ccadic/HackZeGarage/images/20220101_232448.jpg

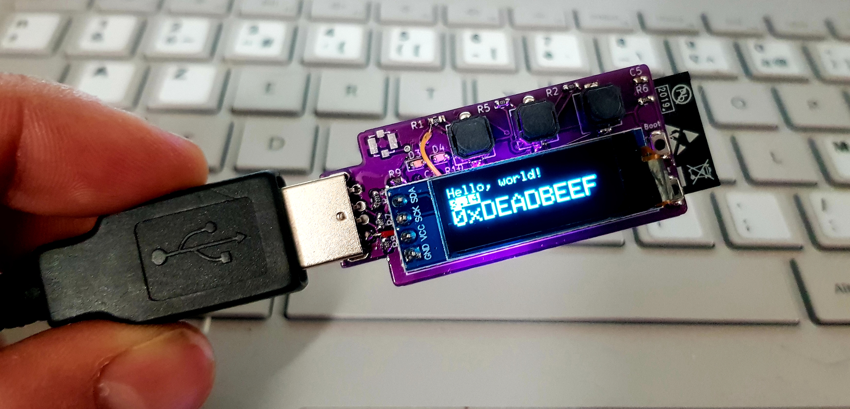
images/20220101_232448.jpg
