ccadic/HackZeGarage/images/20220101_232506.jpg

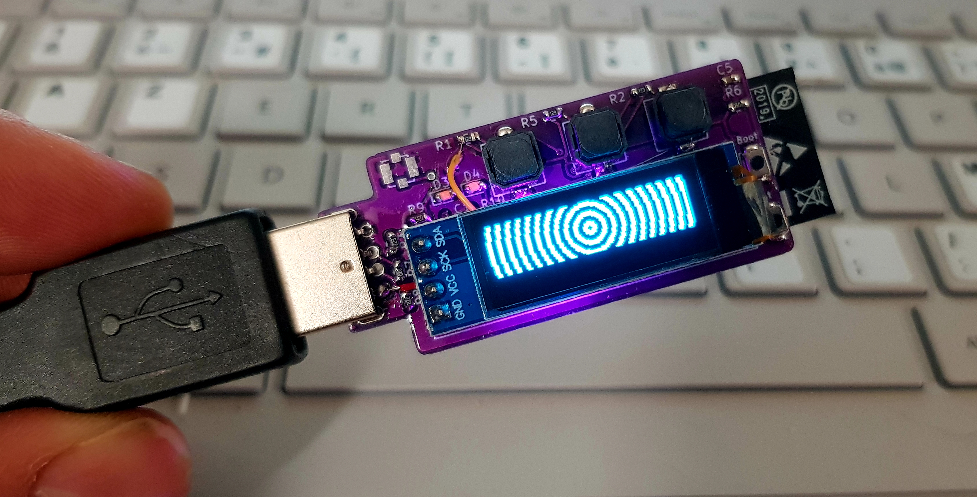
images/20220101_232506.jpg
