ccadic/HackZeGarage/images/20220101_232624.jpg

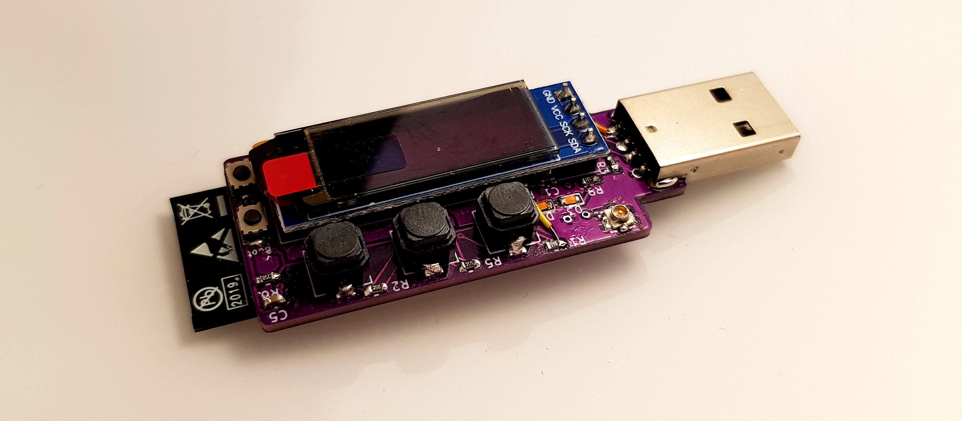
images/20220101_232624.jpg
