ccadic/HackZeGarage/images/20220101_232640.jpg

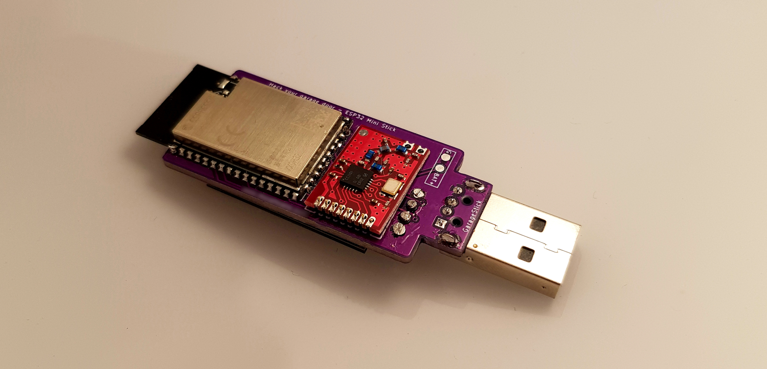
images/20220101_232640.jpg
