ccadic/HackZeGarage/images/20220102_003041.jpg

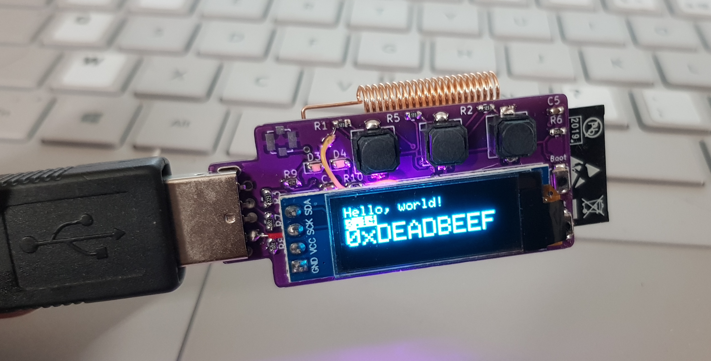
images/20220102_003041.jpg
