ccadic/HackZeGarage/images/20220102_003132.jpg

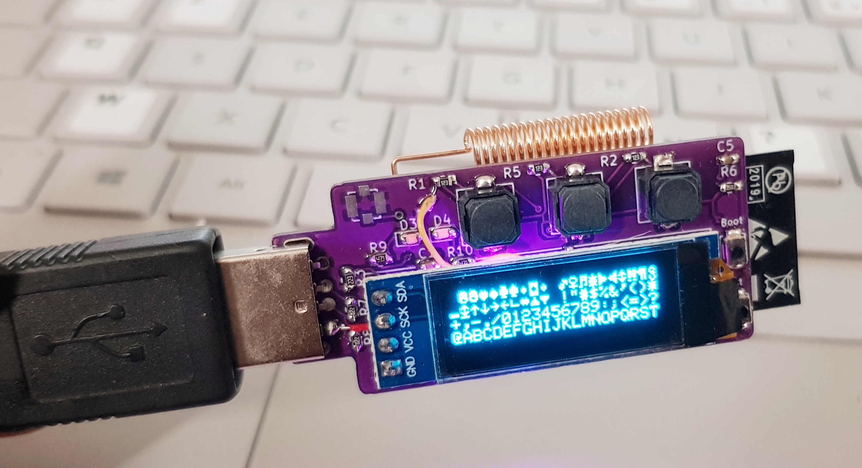
images/20220102_003132.jpg
