ccadic/HackZeGarage/images/20220102_133309.jpg

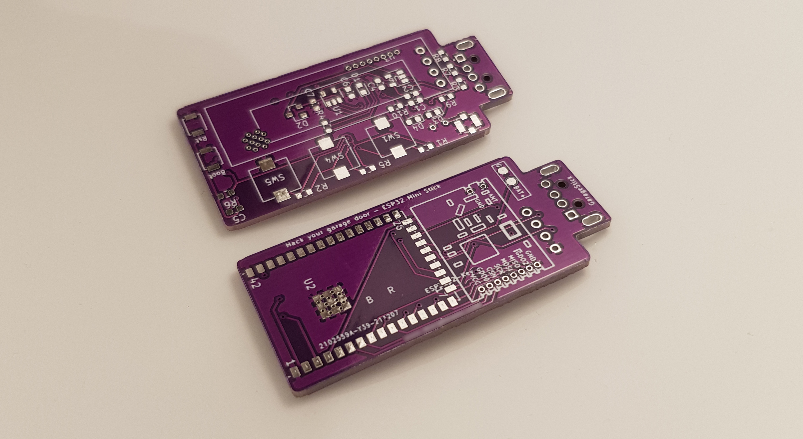
images/20220102_133309.jpg
