ccadic/HackZeGarage/images/20220102_133350.jpg

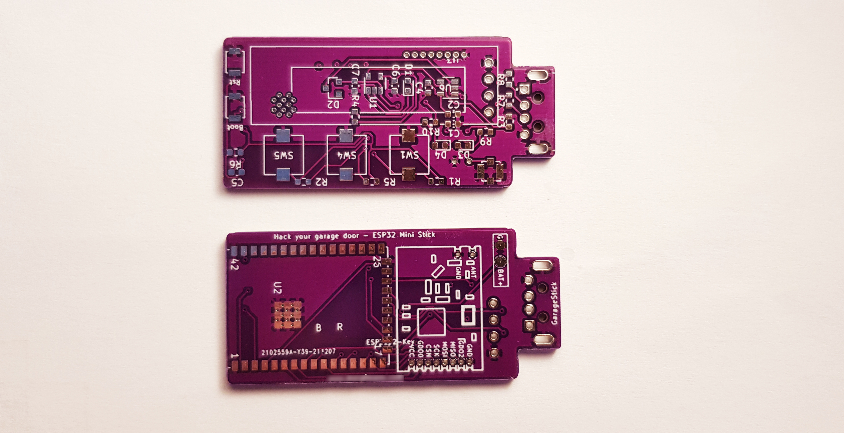
images/20220102_133350.jpg
