ccadic/HackZeGarage/images/keyringgarage3.jpg

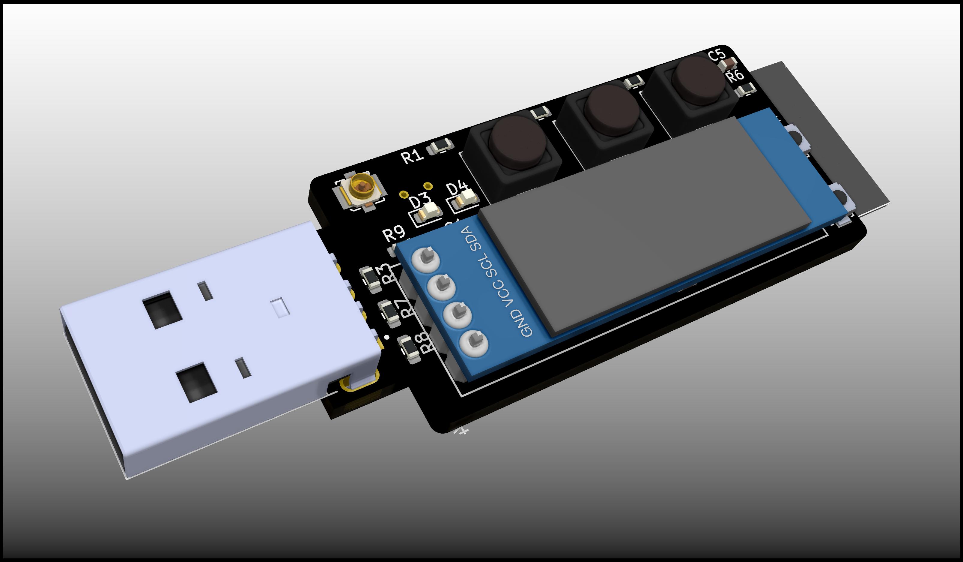
images/keyringgarage3.jpg
