ccadic/HackZeGarage/images/keyringgarage6.jpg

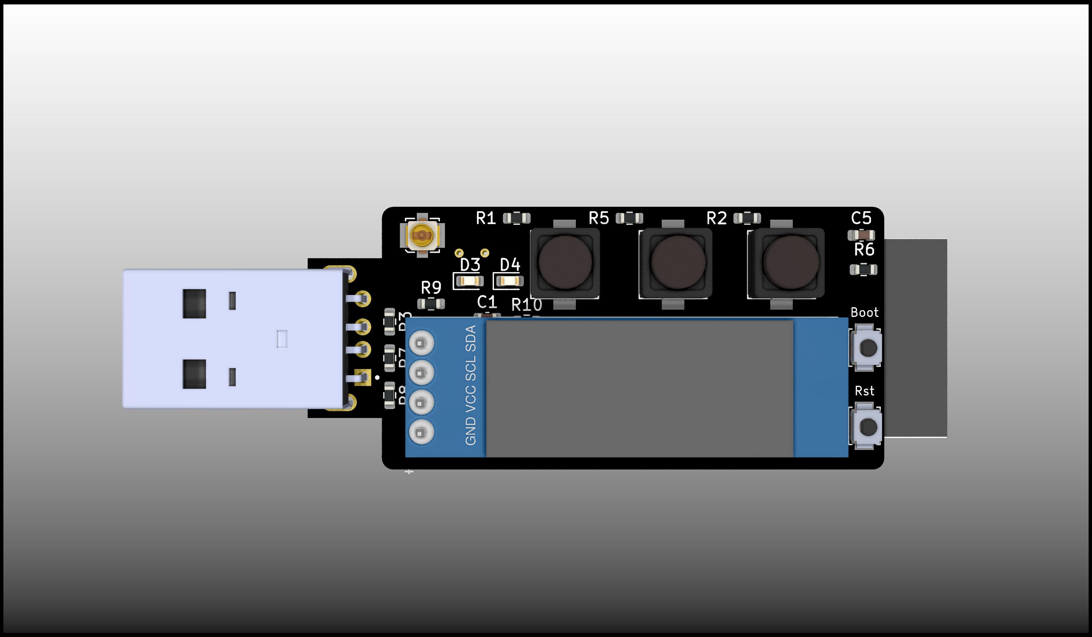
images/keyringgarage6.jpg
