ccadic/HackZeGarage/images/keyringgarage.jpg

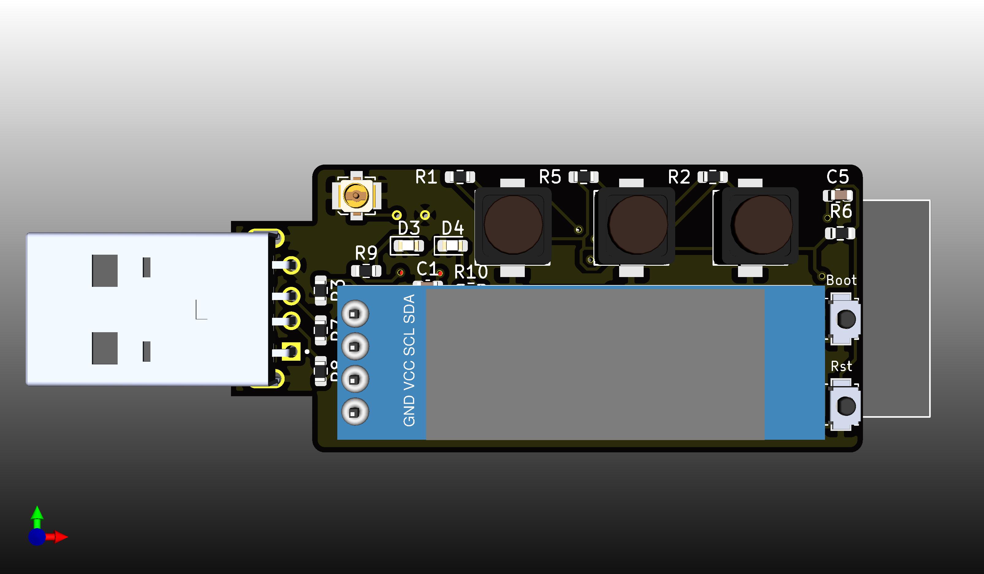
images/keyringgarage.jpg
